lhm0/rotating_display_pico/images/IMG_001.jpg

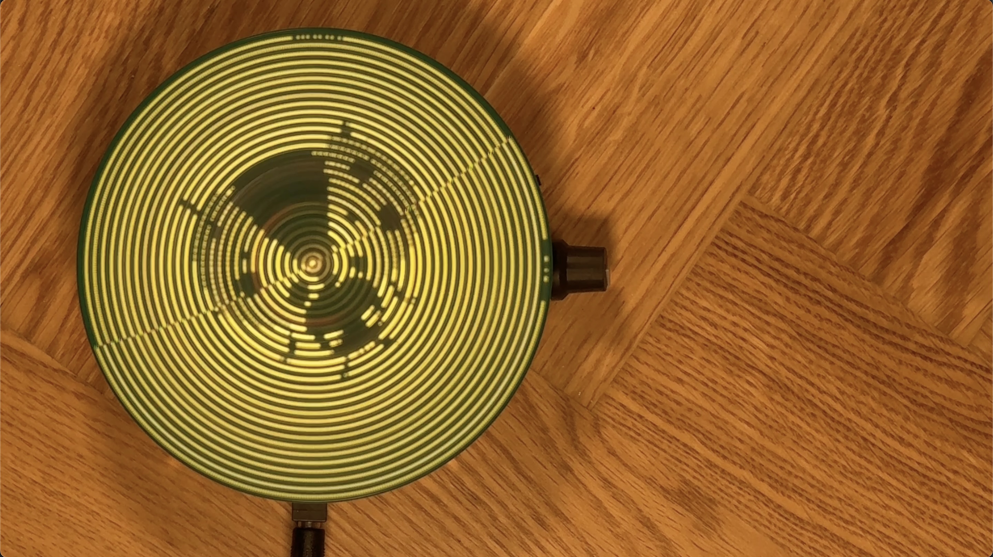
images/IMG_001.jpg
