lhm0/rotating_display_pico/images/IMG_002.jpg

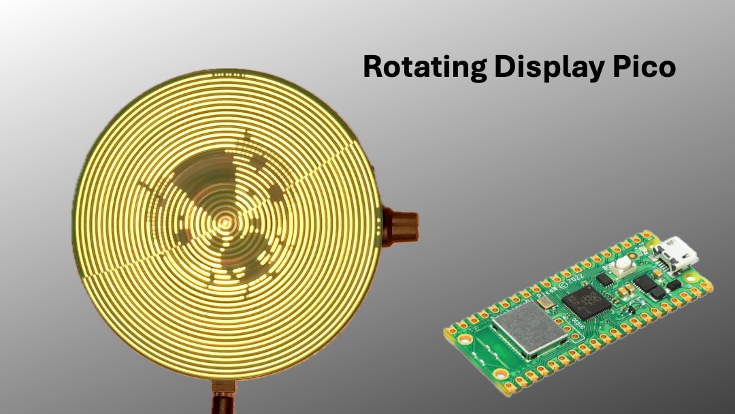
images/IMG_002.jpg
