lhm0/rotating_display_pico/images/IMG_003.jpg

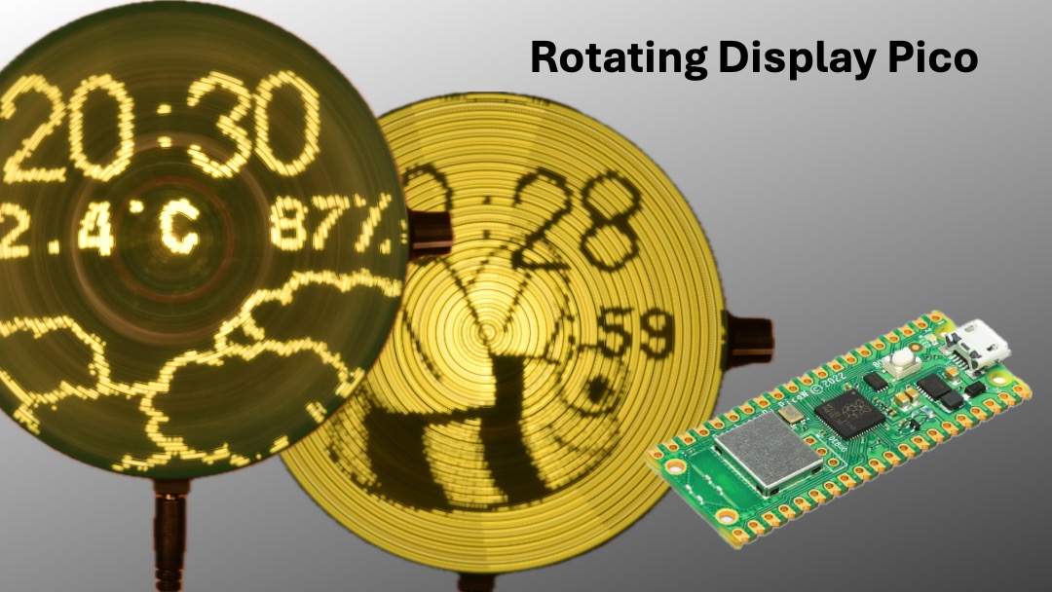
images/IMG_003.jpg
