lhm0/rotating_display_pico/images/IMG_004.jpg

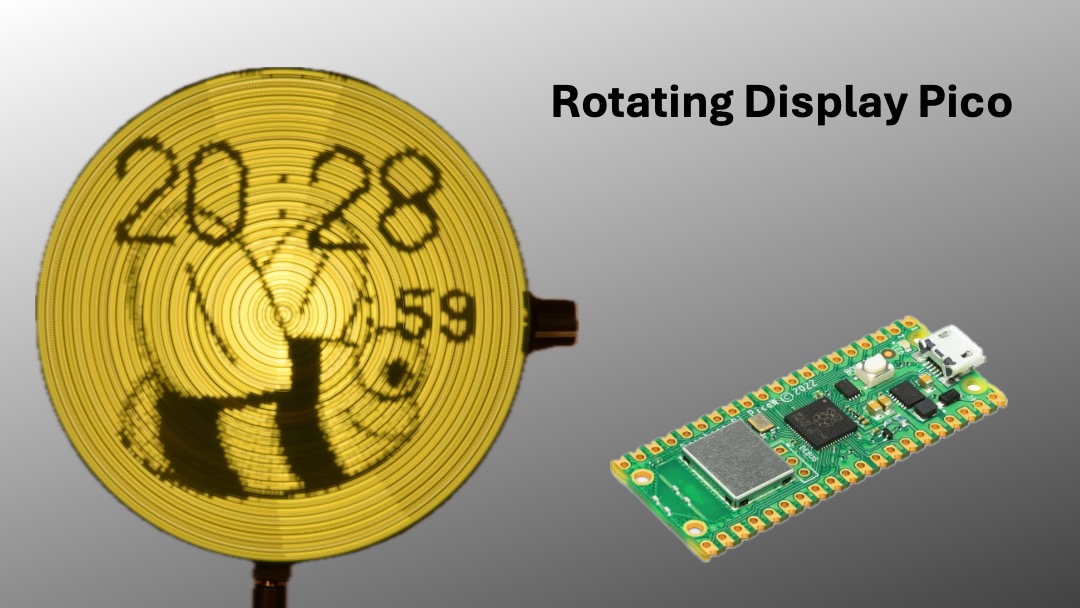
images/IMG_004.jpg
