lhm0/rotating_display_pico/images/IMG_005.jpg

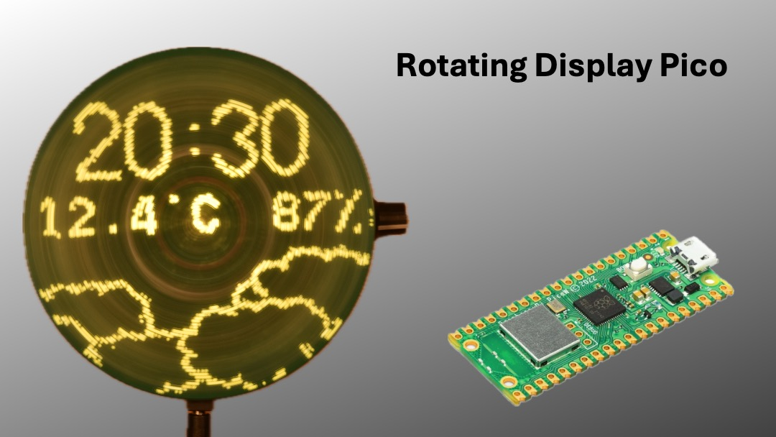
images/IMG_005.jpg
