lhm0/rotating_display_pico/images/IMG_9178.jpg

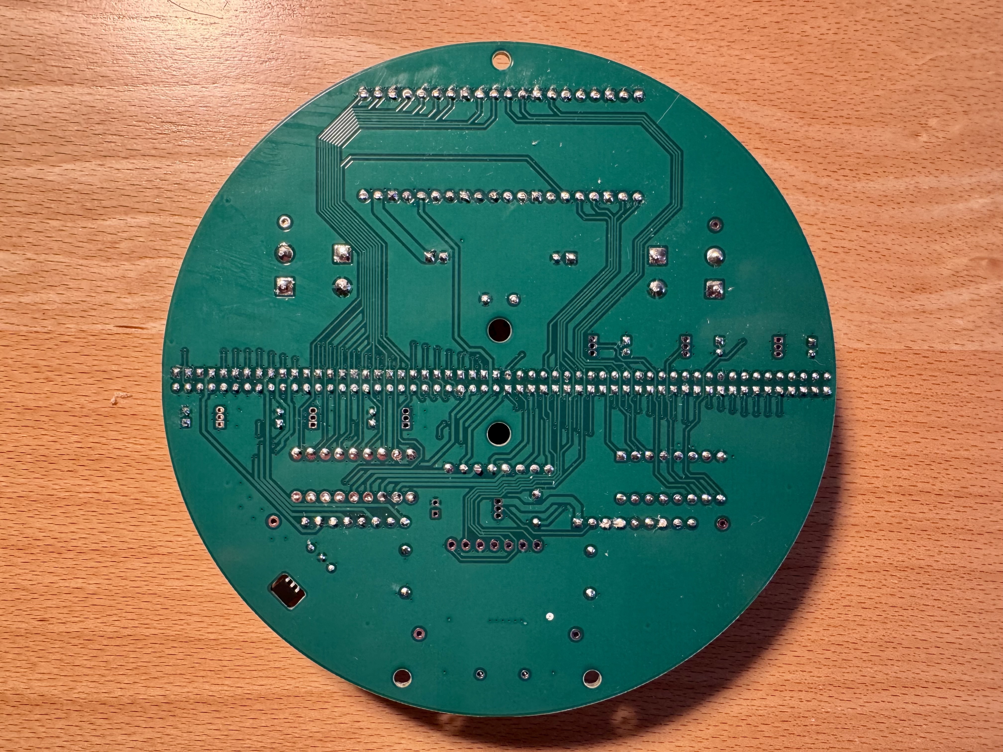
images/IMG_9178.jpg
