lhm0/rotating_display_pico/RDpico_software/src/RD_56mtrafo.h

// =========================================================================================================================================
//                                                 Rotating Display RD40
//                                                    © Ludwin Monz
// License: Creative Commons Attribution - Non-Commercial - Share Alike (CC BY-NC-SA)
// you may use, adapt, share. If you share, "share alike".
// you may not use this software for commercial purposes 
// =========================================================================================================================================


#ifndef RD_56mtrafo_H
#define RD_56mtrafo_H

// ******************************************************************************************************************************************
//
//          in order to display Bitmaps, the rectangular coordinate system of the 110x110 pixel bitmap needs to be transformed 
//          into the polar coordinate system of the display. The below arrays are lookup-tables for this transformation
//
// ******************************************************************************************************************************************

uint8_t trafo_x[56][240] = {
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
};

#endif  
